diegoasanch/RGB-Controller/src/config.h

#pragma once

namespace refreshRate {
    /**
     * All values represent Hz (times per second)
     */
    const float SCREEN = 0.2;
    const float WEATHER = 0.1;
    const unsigned short LED = 150;
}

namespace pins {
    const uint8_t SCREEN_SCL = D1;
    const uint8_t SCREEN_SDA = D2;

    const uint8_t WEATHER_DATA = D3;

    const uint8_t RGB_BLUE = D5;
    const uint8_t RGB_RED = D6;
    const uint8_t RGB_GREEN = D7;
}

namespace device {
    const String VERSION = "v1.3.1";
}
